duncanabraham/thortoise/docs/image-20220526235118895.png

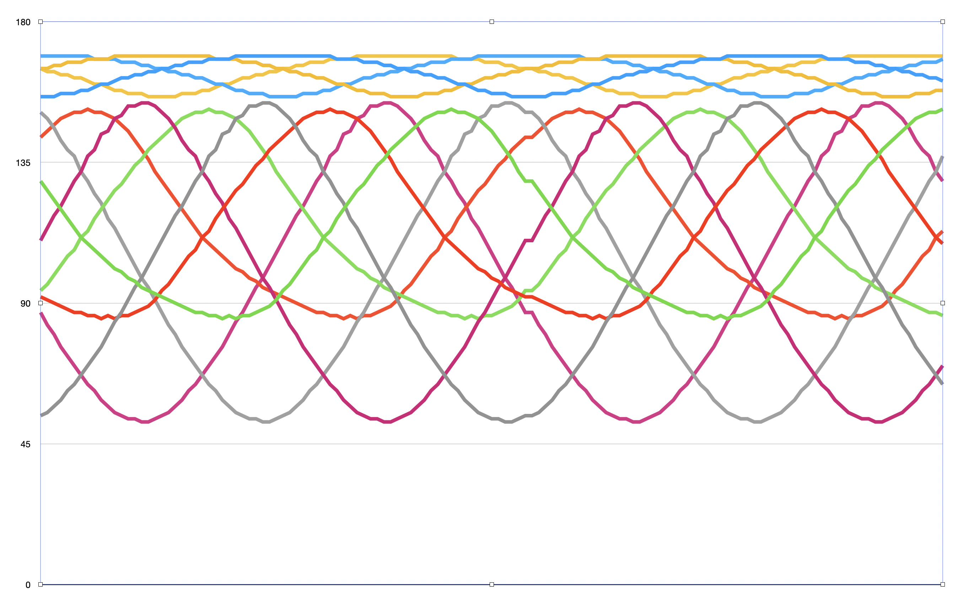
docs/image-20220526235118895.png
