duncanabraham/thortoise/cad/spogget-driveCog-part2.stl

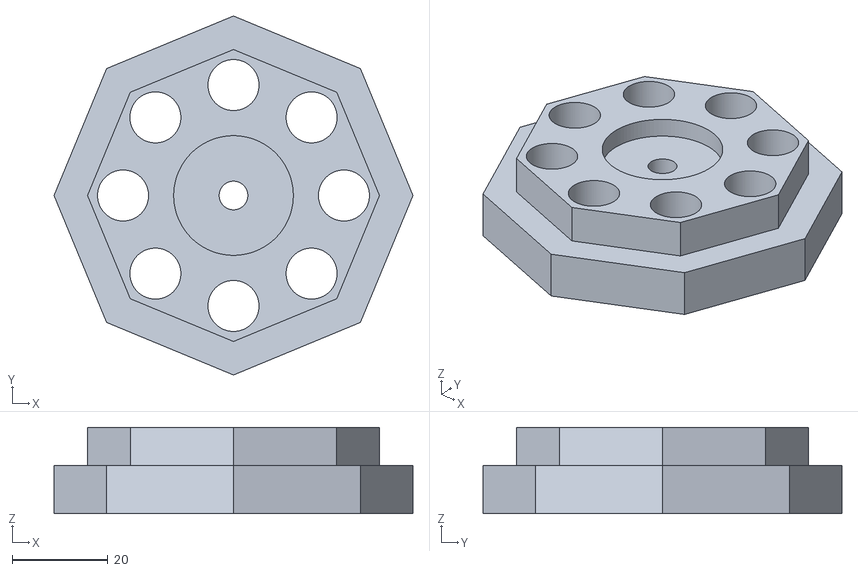
[picture p18: CAD file, 2022-08-27]
cad/spogget-driveCog-part2.stl
75.0 x 75.0 x 18.0
