duncanabraham/thortoise/cad/spogget-cog-part2.stl

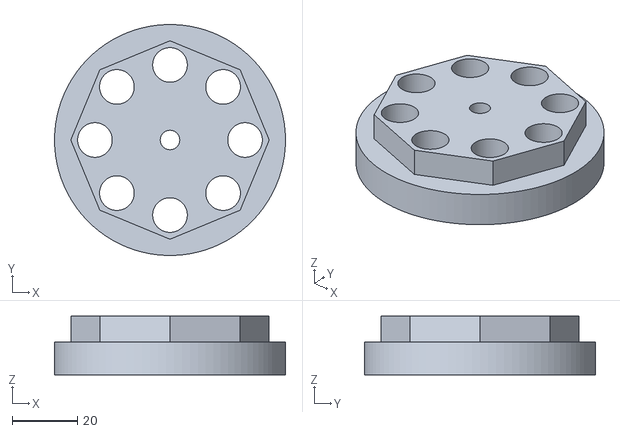
[picture p19: CAD file, 2022-08-27]
cad/spogget-cog-part2.stl
71.0 x 71.0 x 18.0
