duncanabraham/thortoise/cad/drive_spogget.stl

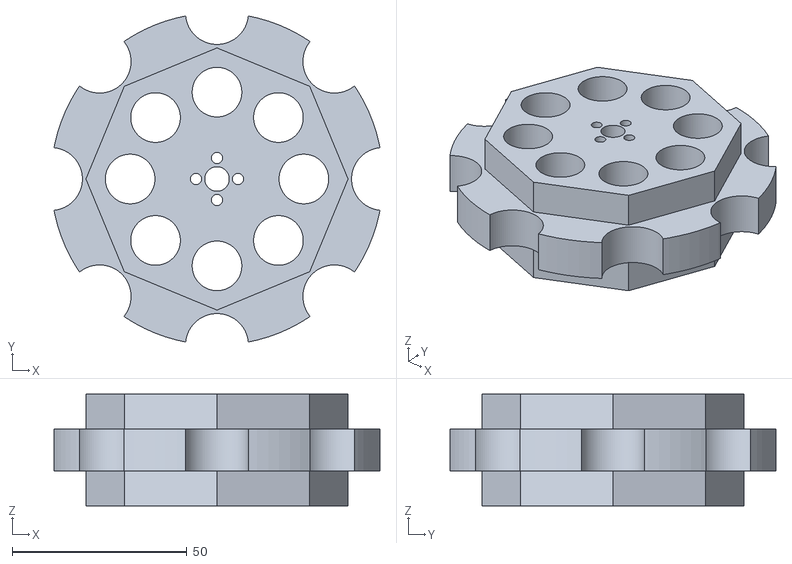
[picture p20: CAD file, 2022-08-27]
cad/drive_spogget.stl
93.2 x 93.3 x 32.0
