duncanabraham/thortoise/cad/spogget-nose.stl

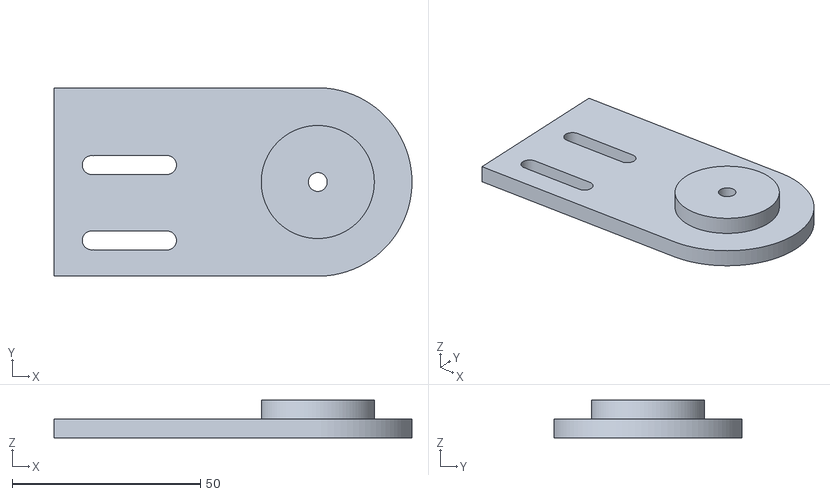
[picture p21: CAD file, 2022-08-27]
cad/spogget-nose.stl
95.0 x 50.0 x 10.0
