duncanabraham/thortoise/cad/spogget_plate.stl

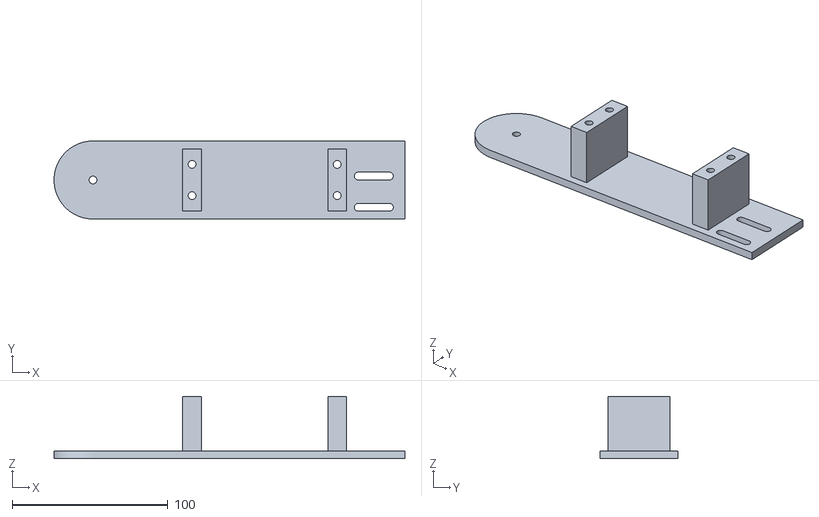
[picture p22: CAD file, 2022-08-23]
cad/spogget_plate.stl
225.0 x 50.0 x 40.0
