duncanabraham/thortoise/cad/spogget-nase.stl

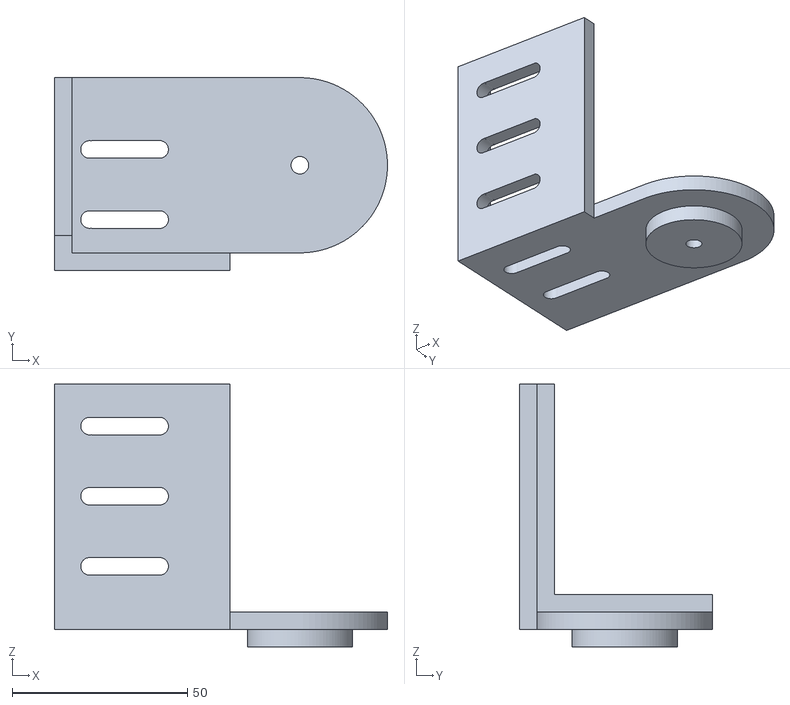
[picture p23: CAD file, 2022-08-23]
cad/spogget-nase.stl
95.0 x 55.0 x 75.0
