duncanabraham/thortoise/cad/spogget-back-plate.stl

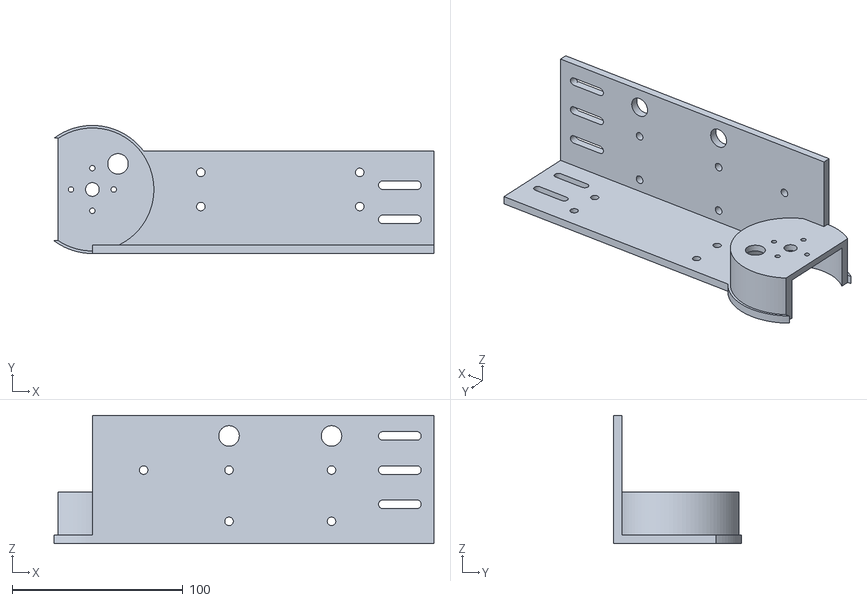
[picture p24: CAD file, 2022-08-23]
cad/spogget-back-plate.stl
222.5 x 75.0 x 75.0
