duncanabraham/thortoise/cad/lightHolder.stl

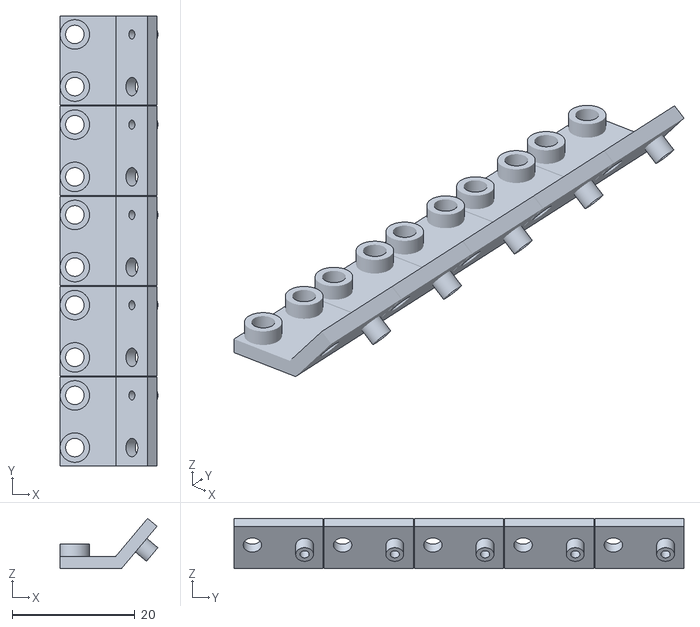
[picture p25: CAD file, 2022-08-21]
cad/lightHolder.stl
15.9 x 73.3 x 8.18
