duncanabraham/thortoise/cad/motorbaseLevel5.stl

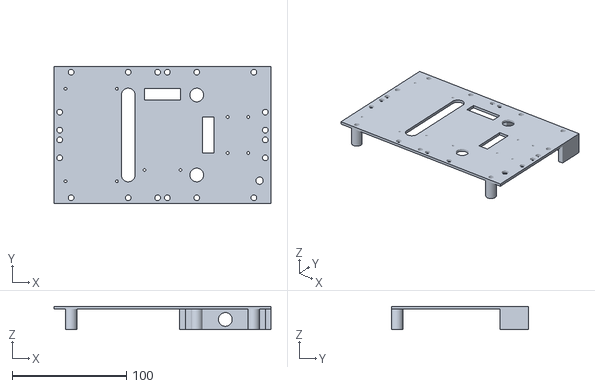
[picture p26: CAD file, 2022-08-21]
cad/motorbaseLevel5.stl
190.0 x 120.0 x 20.5
