duncanabraham/thortoise/cad/motorbaseCameraBracket.stl

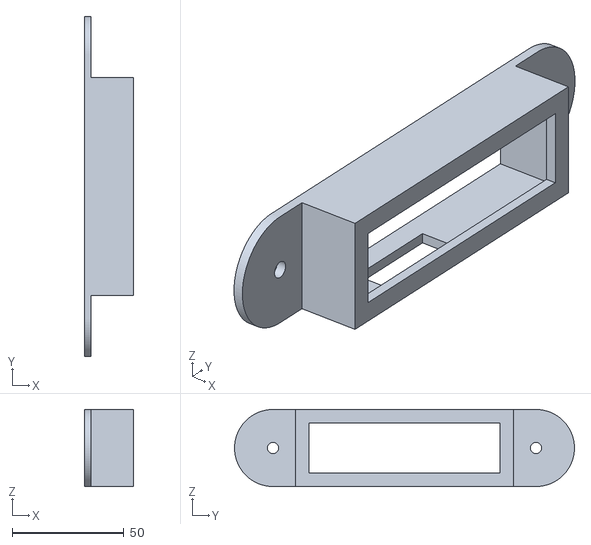
[picture p27: CAD file, 2022-08-19]
cad/motorbaseCameraBracket.stl
21.9 x 151.8 x 34.4
