duncanabraham/thortoise/cad/motorbase.stl

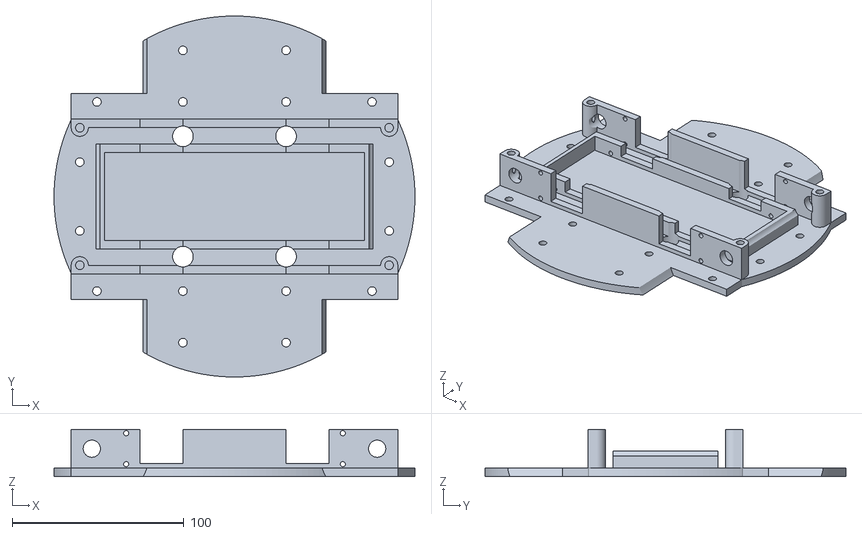
[picture p28: CAD file, 2022-08-16]
cad/motorbase.stl
210.0 x 210.0 x 27.5
