duncanabraham/thortoise/cad/motorbaseLevel4.stl

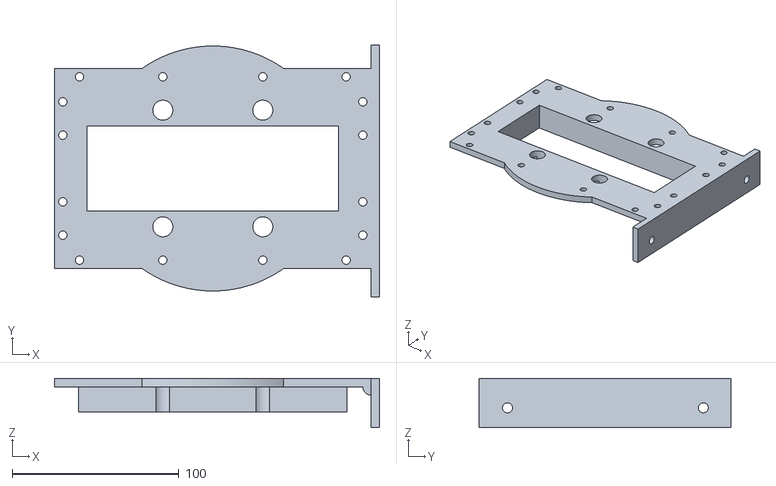
[picture p29: CAD file, 2022-08-16]
cad/motorbaseLevel4.stl
195.0 x 151.0 x 29.4
