duncanabraham/thortoise/cad/motorbaseLevel2.stl

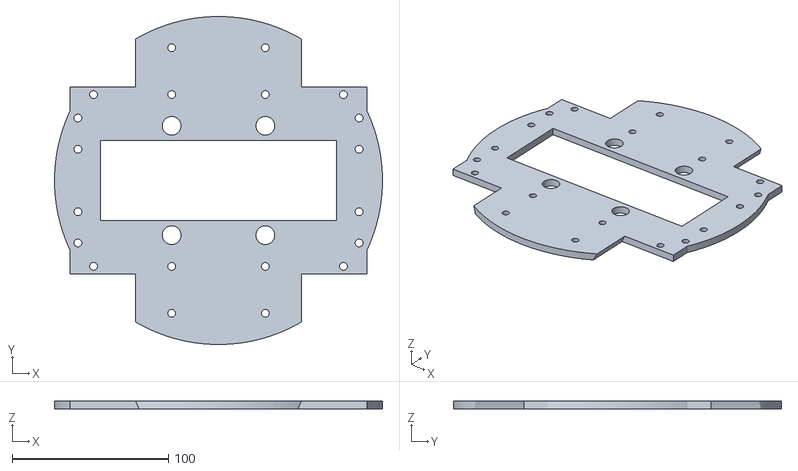
[picture p30: CAD file, 2022-08-16]
cad/motorbaseLevel2.stl
210.0 x 210.0 x 5.00
