duncanabraham/thortoise/cad/motorbaseLevel3.stl

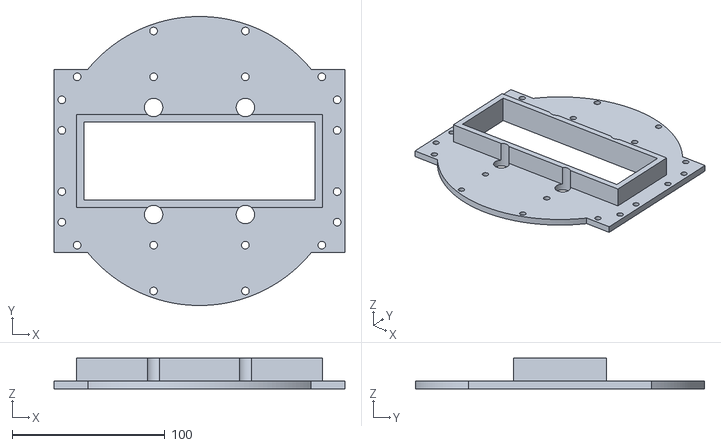
[picture p31: CAD file, 2022-08-16]
cad/motorbaseLevel3.stl
190.0 x 189.0 x 20.0
