duncanabraham/thortoise/cad/motorbaseLid.stl

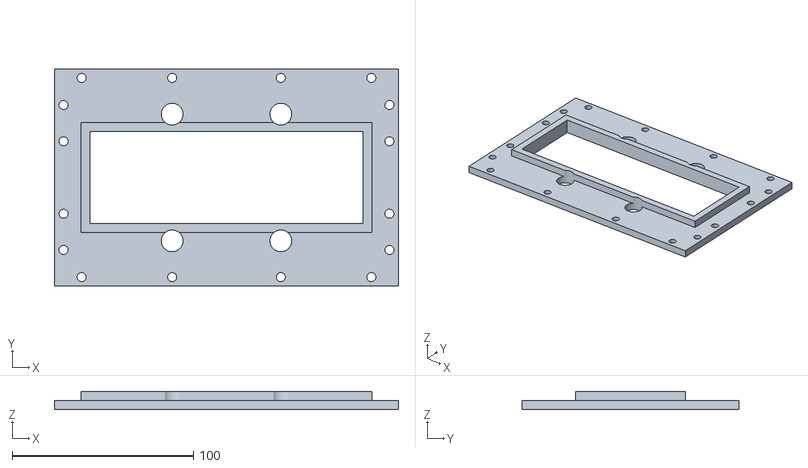
[picture p32: CAD file, 2022-08-12]
cad/motorbaseLid.stl
190.0 x 120.0 x 10.0
