duncanabraham/thortoise/cad/Snow_Track1.STL

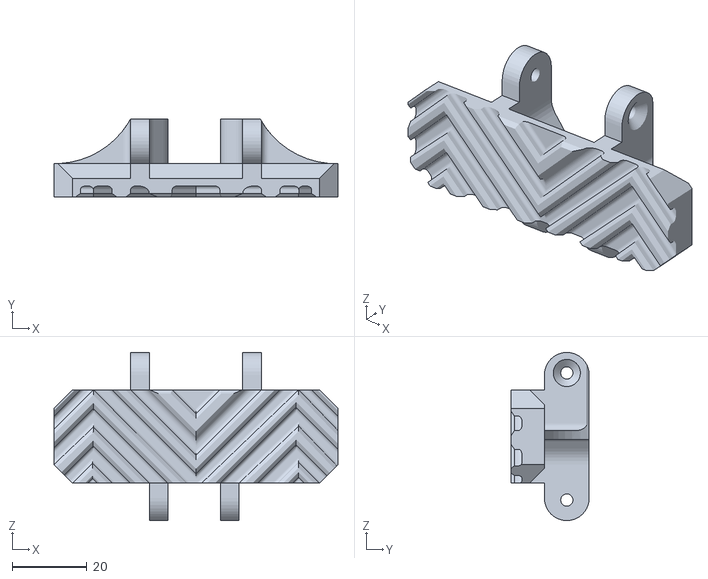
[picture p33: CAD file, 2022-08-12]
cad/Snow_Track1.STL
76.0 x 21.0 x 45.0
