duncanabraham/thortoise/cad/wheel.stl

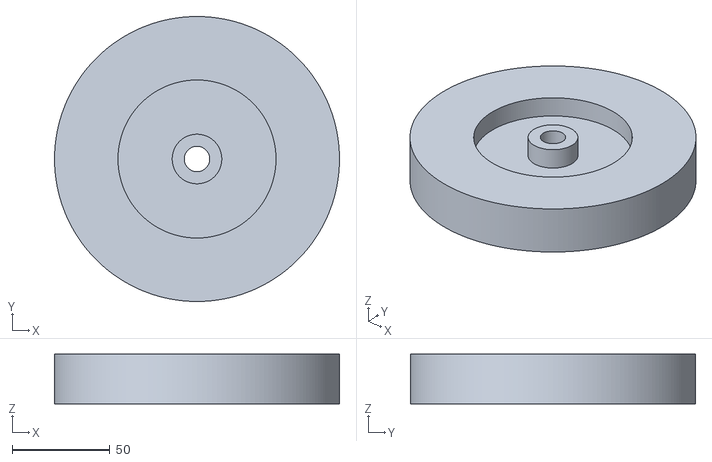
[picture p34: CAD file, 2022-08-08]
cad/wheel.stl
146.0 x 146.0 x 25.6
