duncanabraham/thortoise/cad/box2.stl

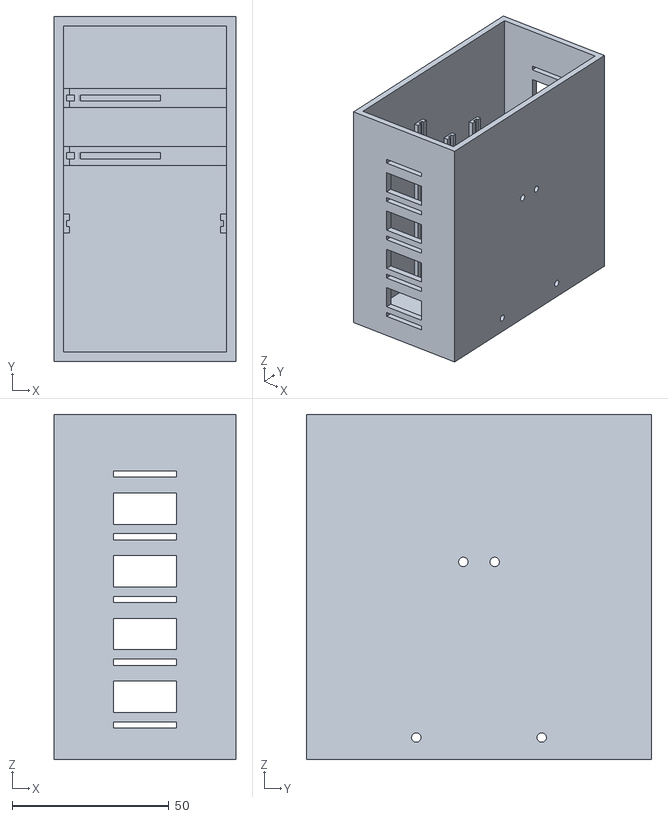
[picture p35: CAD file, 2022-07-31]
cad/box2.stl
58.0 x 110.0 x 110.0
