duncanabraham/thortoise/cad/box4.stl

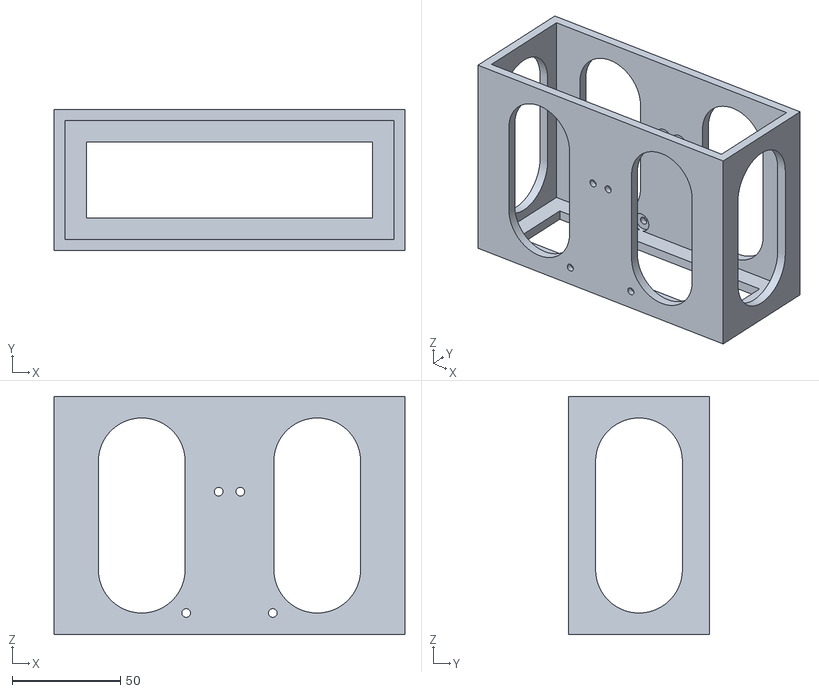
[picture p36: CAD file, 2022-07-31]
cad/box4.stl
162.0 x 65.0 x 110.0
