duncanabraham/thortoise/cad/box3.stl

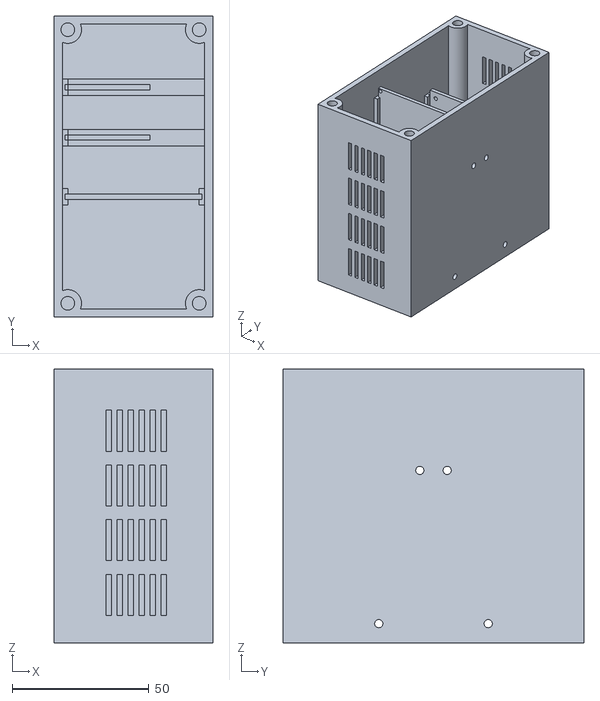
[picture p37: CAD file, 2022-07-31]
cad/box3.stl
58.0 x 110.0 x 100.0
