duncanabraham/thortoise/cad/R_shoulder.stl

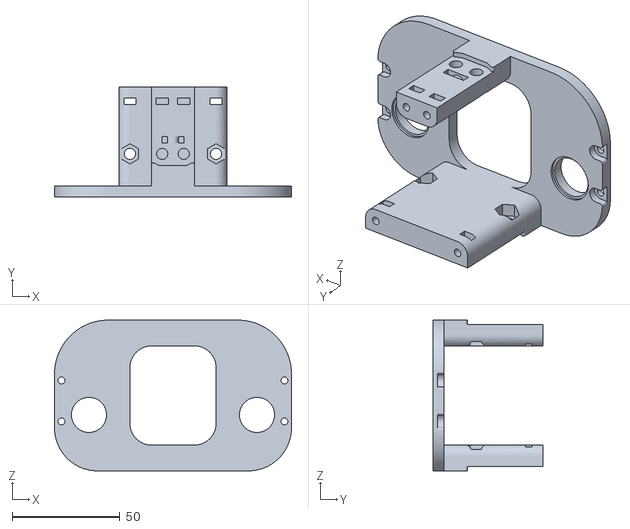
[picture p38: CAD file, 2022-07-25]
cad/R_shoulder.stl
110.0 x 51.0 x 70.0
