duncanabraham/thortoise/cad/F_shoulder.stl

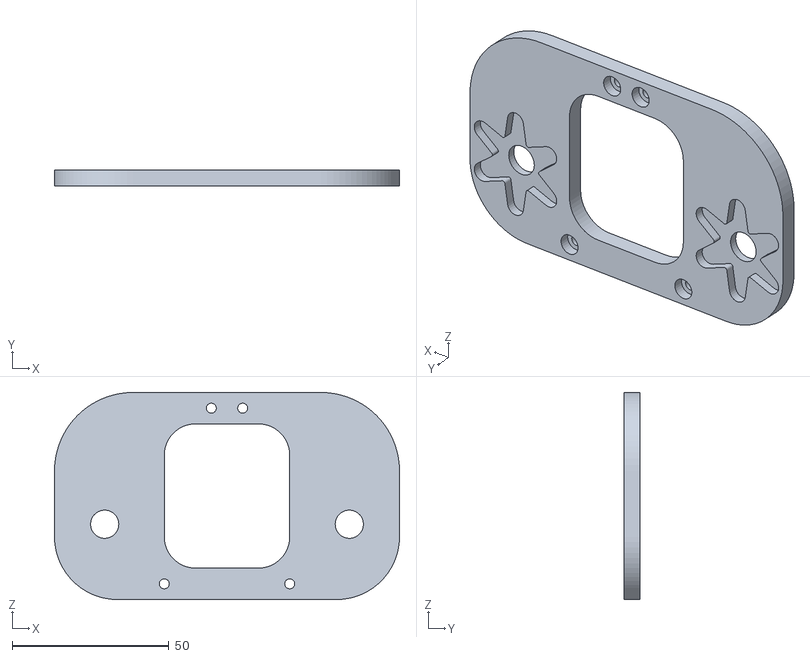
[picture p39: CAD file, 2022-07-25]
cad/F_shoulder.stl
110.0 x 5.00 x 66.0
