duncanabraham/thortoise/cad/box.stl

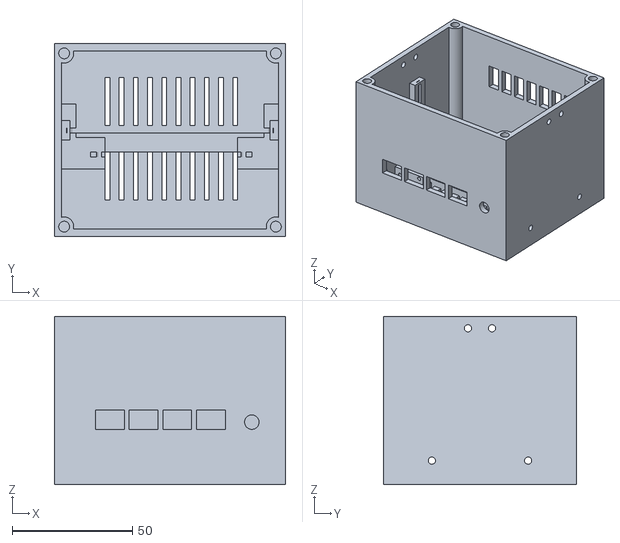
[picture p40: CAD file, 2022-07-24]
cad/box.stl
96.0 x 80.0 x 70.0
