duncanabraham/thortoise/cad/box-lid.stl

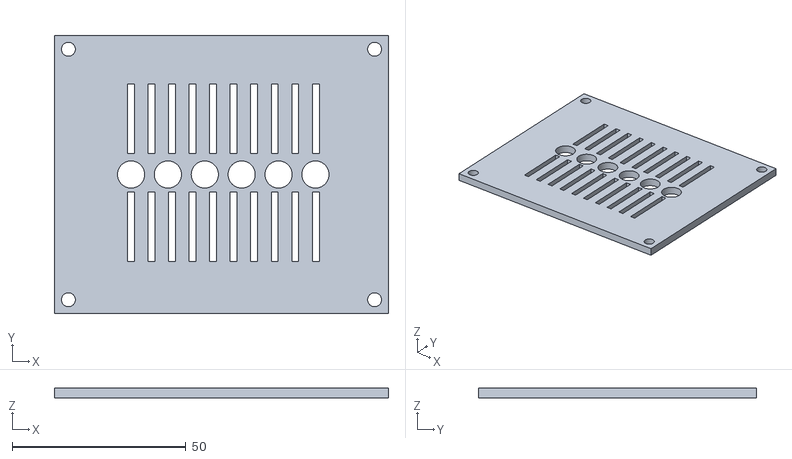
[picture p41: CAD file, 2022-07-24]
cad/box-lid.stl
96.0 x 80.0 x 3.00
