duncanabraham/thortoise/cad/bottomBracket.3mf

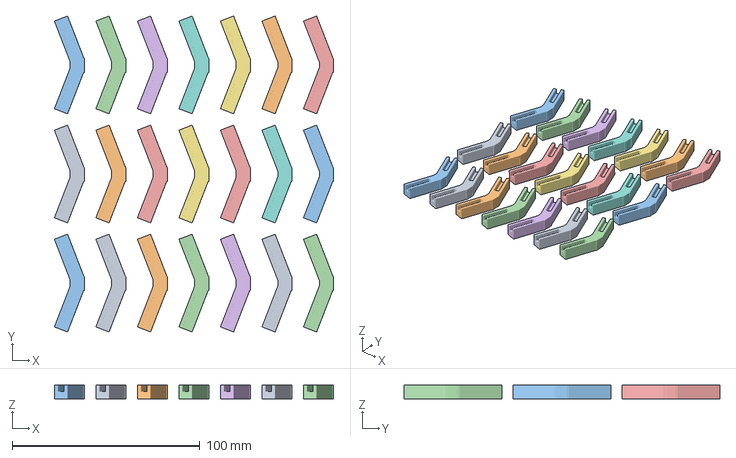
[picture p42: CAD file, 2022-07-20]
cad/bottomBracket.3mf
148.6 x 168.1 x 7.63 mm
bottomBracket.stl x 21
