duncanabraham/thortoise/cad/HexaLeg.3mf

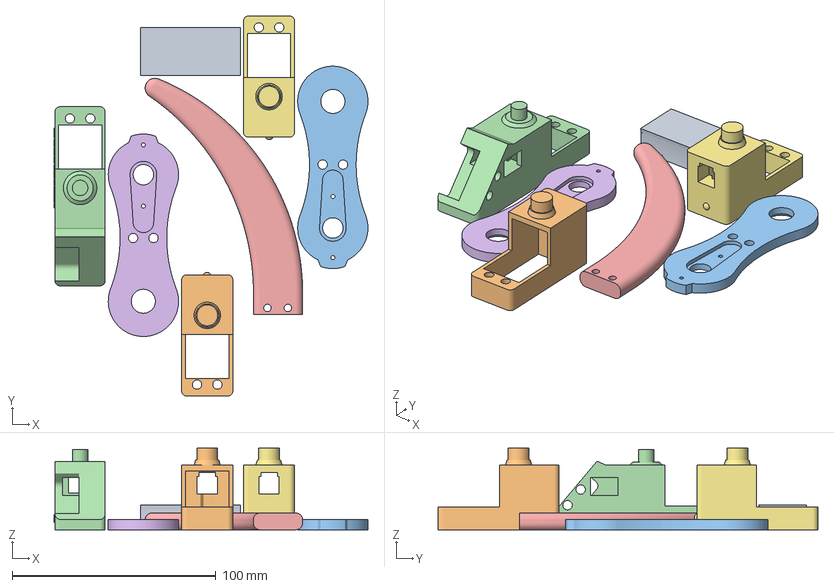
[picture p43: CAD file, 2022-07-20]
cad/HexaLeg.3mf
154.0 x 186.4 x 40.0 mm
6_x_Join.stl
12_x_Leg_B.stl
12_x_Leg_C.stl
6_x_Leg_A.stl
6_x_Leg_D.stl
12_x_Leg_C.stl(1)
12_x_Leg_B.stl(1)
