duncanabraham/thortoise/cad/topBracket.stl

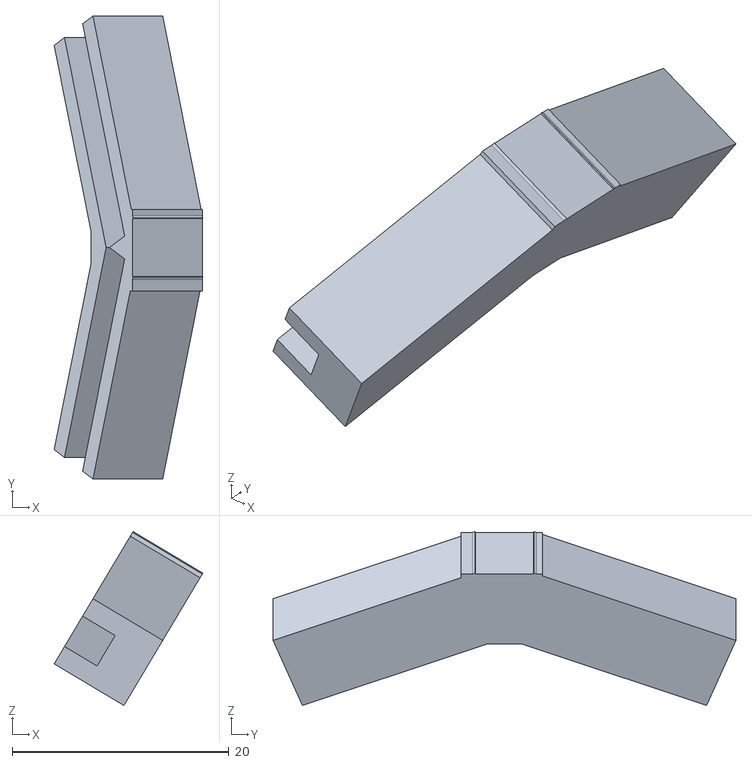
[picture p44: CAD file, 2022-07-20]
cad/topBracket.stl
13.7 x 42.7 x 16.1
