duncanabraham/thortoise/cad/solarcells-2.3mf

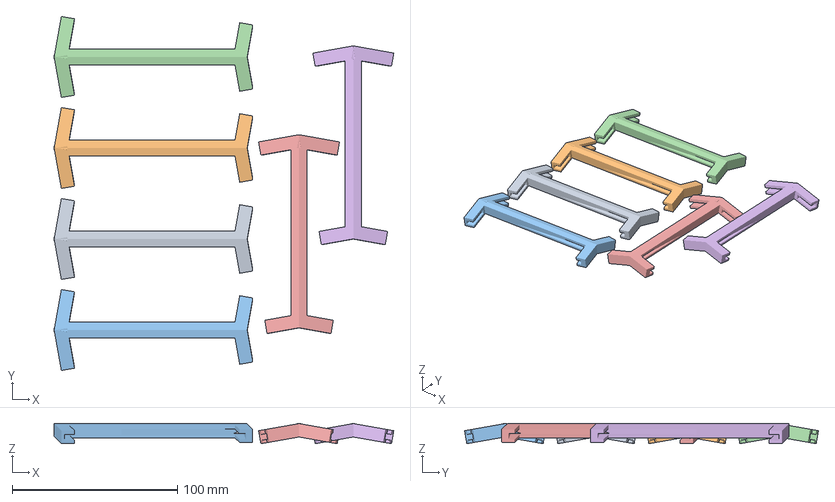
[picture p45: CAD file, 2022-07-14]
cad/solarcells-2.3mf
205.7 x 214.3 x 12.4 mm
solarcells-2.stl x 6
