duncanabraham/thortoise/cad/solarcells-new.stl

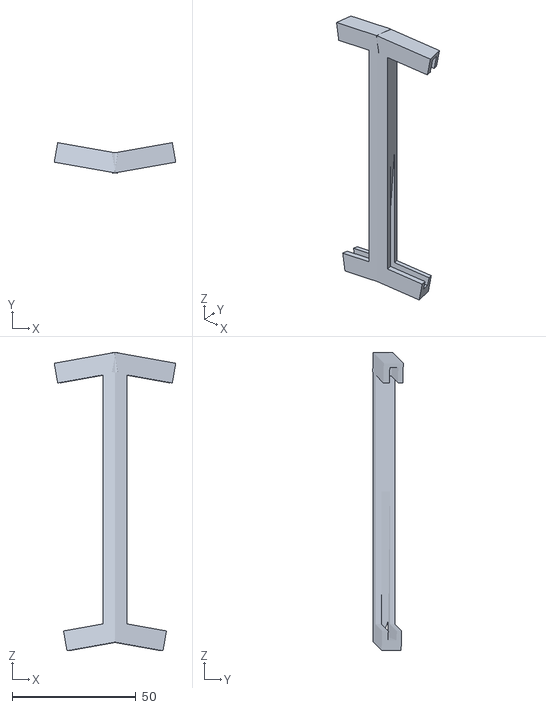
[picture p46: CAD file, 2022-07-14]
cad/solarcells-new.stl
49.0 x 12.4 x 120.2
