duncanabraham/thortoise/cad/solarcells.stl

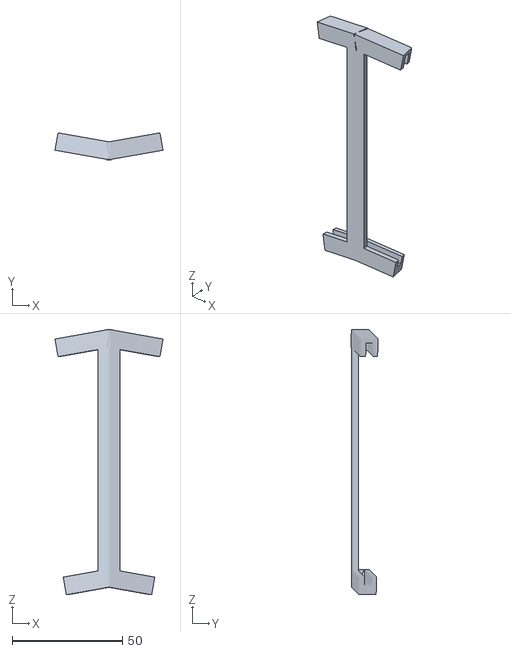
[picture p47: CAD file, 2022-07-11]
cad/solarcells.stl
49.0 x 12.4 x 120.2
