duncanabraham/thortoise/cad/baseplate.stl

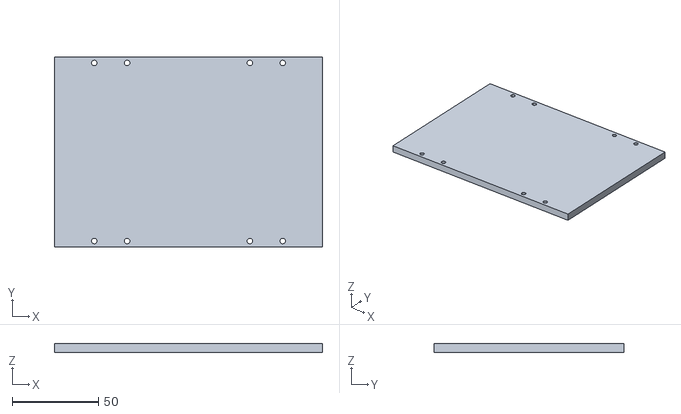
[picture p48: CAD file, 2022-06-16]
cad/baseplate.stl
155.0 x 110.0 x 5.00
