duncanabraham/thortoise/cad/basicBase.stl

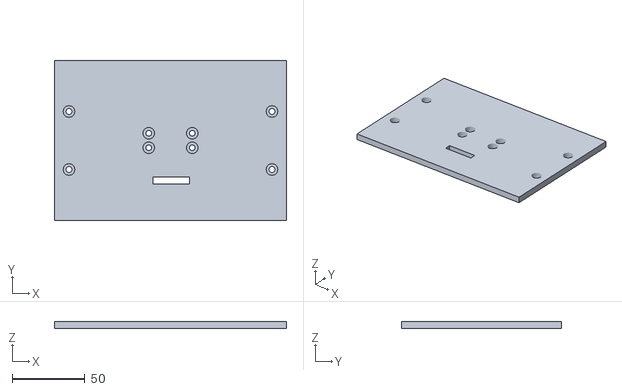
[picture p49: CAD file, 2022-06-14]
cad/basicBase.stl
160.0 x 110.0 x 5.00
