duncanabraham/thortoise/cad/topLid.stl

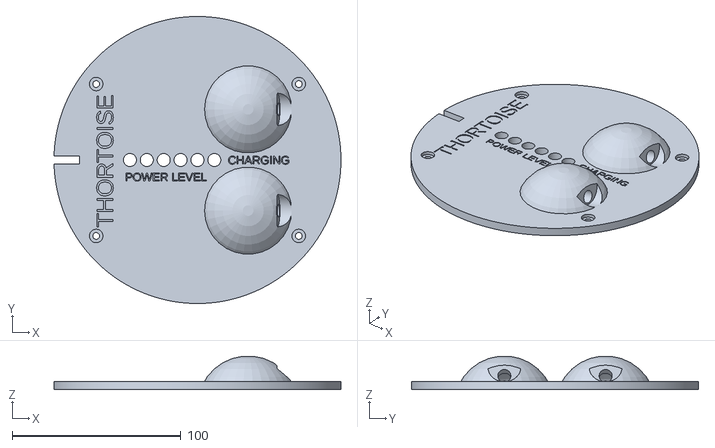
[picture p50: CAD file, 2022-06-12]
cad/topLid.stl
170.0 x 170.0 x 19.8
