duncanabraham/thortoise/cad/brackets.scad

// Brackets for solar panels

// 17 panels in a circle
