duncanabraham/thortoise/cad/femur.scad

import("/Users/duncanabraham/Downloads/STL_files/FEMUR/inner femur_m_x2.stl");
import("/Users/duncanabraham/Downloads/STL_files/FEMUR/inner femur_x2.stl");
import("/Users/duncanabraham/Downloads/STL_files/FEMUR/outer femur_m_x2.stl");
import("/Users/duncanabraham/Downloads/STL_files/FEMUR/outer femur_x2.stl");
import("/Users/duncanabraham/Downloads/STL_files/FEMUR/spacer femur_m_x2.stl");
import("/Users/duncanabraham/Downloads/STL_files/FEMUR/spacer femur_x2.stl");


import("/Users/duncanabraham/Downloads/STL_files/COXA/back fork_x2.stl");
import("/Users/duncanabraham/Downloads/STL_files/COXA/front fork_x2.stl");
import("/Users/duncanabraham/Downloads/STL_files/COXA/servo clamp_x2.stl");
import("/Users/duncanabraham/Downloads/STL_files/COXA/servo clamp w-hole_x2.stl");
import("/Users/duncanabraham/Downloads/STL_files/COXA/horn holder_x4.stl");
import("/Users/duncanabraham/Downloads/STL_files/COXA/bearing holder_x4.stl");

import("/Users/duncanabraham/Downloads/STL_files/TIBIA/inner_tibia_m_x2.stl");
import("/Users/duncanabraham/Downloads/STL_files/TIBIA/inner_tibia_x2.stl");
import("/Users/duncanabraham/Downloads/STL_files/TIBIA/outer_tibia_m_x2.stl");
import("/Users/duncanabraham/Downloads/STL_files/TIBIA/outer_tibia_x2.stl");
import("/Users/duncanabraham/Downloads/STL_files/TIBIA/TPU_contact_x4.stl");

//import("/Users/duncanabraham/Downloads/STL_files/back.stl");
//import("/Users/duncanabraham/Downloads/STL_files/front.stl");
