duncanabraham/thortoise/cad/tracks.scad

import("Snow_Track1.STL");
